adamples/VU_meter/images/journal/2017-11-23.jpeg

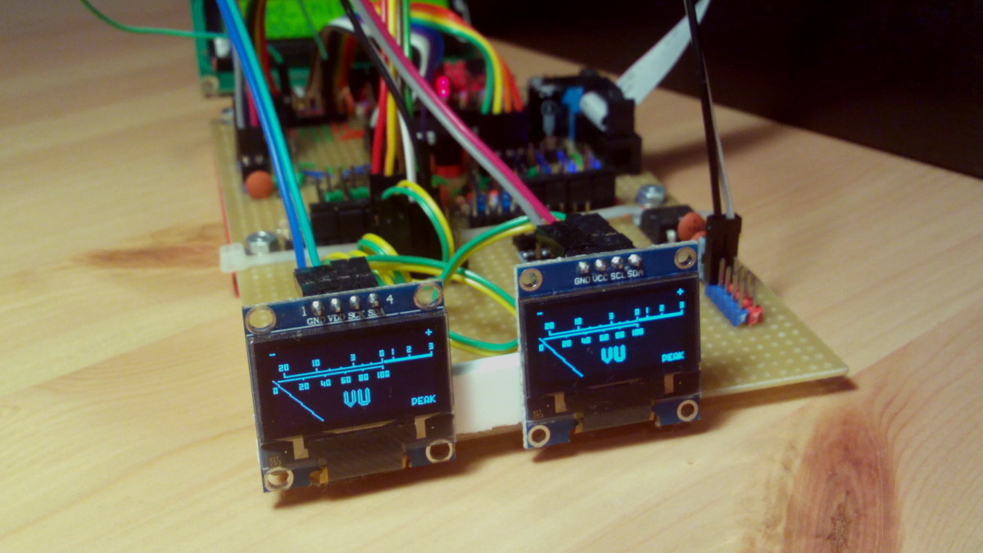
images/journal/2017-11-23.jpeg
