adamples/VU_meter/src/oled.c

#include "config.h"
#include "oled.h"
#include "utils.h"


#if OLED_DRIVER == OLED_DRIVER_SSD1305
#include "oled_ssd1305.c"
#elif OLED_DRIVER == OLED_DRIVER_SSD1306
#include "oled_ssd1306.c"
#elif OLED_DRIVER == OLED_DRIVER_SSD1309
#include "oled_ssd1309.c"
#else
#include "oled_sh1106.c"
#endif


void oled_reset()
{
  delay_ms(10);
  OLED_RESET_DDR |= _BV(OLED_RESET_P);
  OLED_RESET_PORT &= ~_BV(OLED_RESET_P);
  delay_ms(10);
  OLED_RESET_PORT |= _BV(OLED_RESET_P);
  delay_ms(10);
}
