adamples/VU_meter/src/watermark.c

#include <stdint.h>
#include <avr/pgmspace.h>

const uint8_t WATERMARK[34] PROGMEM = {
  0x20, /* = width */
  0x08, /* = height */
  0x60, 0x48, 0x78, 0x40, 0x78, 0x48, 0x7c, 0x40, 0x60, 0x48, 0x78, 0x40, 0x78, 0x08, 0x78, 0x08,
  0x78, 0x40, 0x00, 0xf8, 0x48, 0x78, 0x00, 0x7c, 0x40, 0x78, 0x48, 0x58, 0x40, 0x58, 0x48, 0x68,
  };
