adamples/VU_meter/src/needle_coordinates.c

#include "needle_coordinates.h"
#include <stdint.h>
#include <avr/pgmspace.h>

const needle_coordinates_t NEEDLE_COORDINATES[NEEDLE_RESOLUTION] PROGMEM = {
  {   0,  23 },
  {   1,  23 },
  {   2,  22 },
  {   3,  21 },
  {   3,  21 },
  {   4,  20 },
  {   5,  19 },
  {   6,  19 },
  {   7,  18 },
  {   8,  17 },
  {   9,  17 },
  {  10,  16 },
  {  10,  16 },
  {  11,  15 },
  {  12,  14 },
  {  13,  14 },
  {  14,  13 },
  {  15,  13 },
  {  16,  12 },
  {  17,  12 },
  {  18,  11 },
  {  19,  11 },
  {  20,  10 },
  {  21,  10 },
  {  22,   9 },
  {  23,   9 },
  {  24,   8 },
  {  25,   8 },
  {  26,   7 },
  {  27,   7 },
  {  28,   6 },
  {  29,   6 },
  {  30,   6 },
  {  31,   5 },
  {  32,   5 },
  {  33,   5 },
  {  34,   4 },
  {  35,   4 },
  {  36,   4 },
  {  37,   3 },
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
};
